tb8-5/12VAC-Dual-Output-Buck-Power-Supply-PCB/02_ltspice/bridge_rectifier_schematic.asc

12VAC: voltage; SINE(0 16.97 60)
C1: cap; Smoothing Capacitor
D1: diode; 1N4007
D2: diode; 1N4007
D3: diode; 1N4007
D4: diode; 1N4007
R1: res; Load Resistor
Named nets: DC_Out, 0, AC1, AC2
Bridge Rectifier in LTspice
.tran 60ms
